ondiiik/meteoink/graphics/bitmap/png/gs/greetings.png

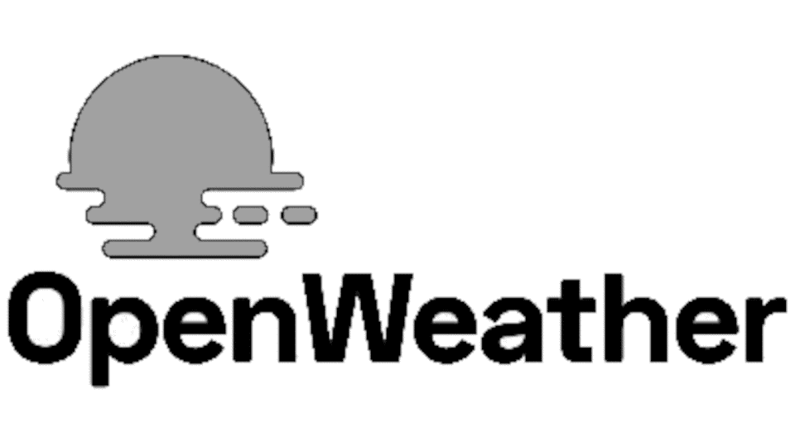
graphics/bitmap/png/gs/greetings.png
