ondiiik/meteoink/graphics/bitmap/wind/acep/wa430.png

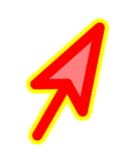
graphics/bitmap/wind/acep/wa430.png
