ondiiik/meteoink/graphics/bitmap/wind/acep/wa445.png

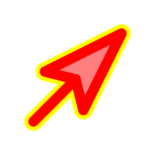
graphics/bitmap/wind/acep/wa445.png
