ondiiik/meteoink/graphics/bitmap/wind/acep/wa460.png

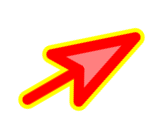
graphics/bitmap/wind/acep/wa460.png
