ondiiik/meteoink/graphics/bitmap/wind/acep/wa4120.png

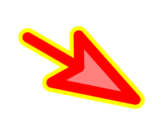
graphics/bitmap/wind/acep/wa4120.png
