ondiiik/meteoink/graphics/bitmap/wind/acep/wa4135.png

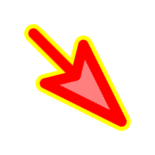
graphics/bitmap/wind/acep/wa4135.png
