ondiiik/meteoink/graphics/bitmap/wind/acep/wa4150.png

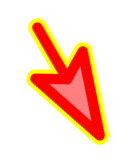
graphics/bitmap/wind/acep/wa4150.png
