ondiiik/meteoink/graphics/bitmap/wind/acep/wa4210.png

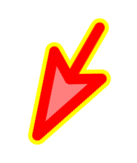
graphics/bitmap/wind/acep/wa4210.png
