ondiiik/meteoink/graphics/bitmap/wind/acep/wa4225.png

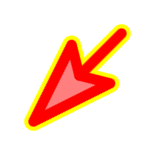
graphics/bitmap/wind/acep/wa4225.png
