ondiiik/meteoink/graphics/bitmap/wind/acep/wa4240.png

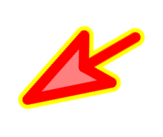
graphics/bitmap/wind/acep/wa4240.png
