ondiiik/meteoink/graphics/bitmap/wind/acep/wa4300.png

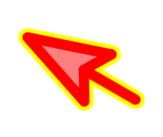
graphics/bitmap/wind/acep/wa4300.png
