ondiiik/meteoink/graphics/bitmap/wind/acep/wa4315.png

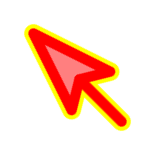
graphics/bitmap/wind/acep/wa4315.png
