ondiiik/meteoink/graphics/bitmap/wind/acep/wa4330.png

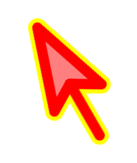
graphics/bitmap/wind/acep/wa4330.png
