ondiiik/meteoink/simulator/main.py

from os import stat

try:
    stat("bitmaps")

    from ulogging import getLogger, dump_exception

    logger = getLogger("main")

    try:
        logger.info("Starting the application ...")
        from app import run

        run()

    except KeyboardInterrupt as e:
        logger.info("Interrupted by keyboard ...")
    except BaseException as e:
        dump_exception("!!! APPLICATION ERROR - REBOOTING !!!", e)
        import machine

        machine.reset()
except OSError:
    print("##############################################")
    print("### Please upload bitmaps (folder bitmaps) ###")
    print("##############################################")
