ondiiik/meteoink/simulator/web/page/index.py

from ulogging import getLogger

logger = getLogger(__name__)

from config import beep, location, connection, spot, temp, vbat, behavior, time, api
from battery import battery
from lang import trn
import web


def index(page):
    _pg_loc(page)
    _pg_wifi(page)
    _pg_set(page)

    page.heading(2, trn("Misc"))
    page.button(trn("Go to travel mode"), "zzz")
    page.button(trn("Go to normal mode"), "reset")


def _pg_loc(page):
    page.heading(2, trn("Locations setup"))

    with page.table(
        (trn("Location"), trn("Latitude"), trn("Longitude"), "", ""),
        'frame="hsides"',
        'style="text-align:left"',
    ) as table:
        for i in location["locations"]:
            idx = {"idx": location["locations"].index(i)}
            table.row(
                (
                    i["name"],
                    f"{i['lat']:.7f}N",
                    f"{i['lon']:.7f}E",
                    web.button(trn("Edit"), "locedt", idx),
                    web.button(trn("Delete"), "locdlt", idx),
                ),
                web.SPACES,
            )

    page.br()
    page.button(trn("Add new location"), "locnew")
    page.br()


def _pg_wifi(page):
    page.heading(2, trn("WiFi setup"))
    with page.table(
        ("SSID", "BSSID", trn("Location"), "", ""),
        'frame="hsides"',
        'style="text-align:left"',
    ) as table:
        for i in connection["connections"]:
            if i["bssid"] is None:
                bssid = ""
            else:
                bssid = i["bssid"]

            idx = {"idx": connection["connections"].index(i)}
            loc = int(i["location"])
            table.row(
                (
                    i["ssid"],
                    bssid,
                    (
                        location["locations"][loc]["name"]
                        if loc < len(location["locations"])
                        else "..."
                    ),
                    web.button(trn("Edit"), "wifiedt", idx),
                    web.button(trn("Delete"), "wifidlt", idx),
                ),
                web.SPACES,
            )

    page.br()
    page.button(trn("Add new WiFi"), "wifinew")
    page.br()


def _pg_set(page):
    page.heading(2, trn("Confort temperatures"))
    with page.table(None, 'frame="hsides"') as table:
        table.row(
            (trn("Indoor high"), "{:.1f} °C".format(temp["indoor_high"])), web.SPACES
        )
        table.row(
            (trn("Outdoor high"), "{:.1f} °C".format(temp["outdoor_high"])), web.SPACES
        )
        table.row(
            (trn("Outdoor low"), "{:.1f} °C".format(temp["outdoor_low"])), web.SPACES
        )
        table.row((web.button(trn("Edit temperatures"), "tempedt"), ""), web.SPACES)

    page.heading(2, trn("Alerts"))
    with page.table(None, 'frame="hsides"') as table:
        table.row(
            (
                trn("Outside temperature balanced"),
                web.button_enable(beep["temp_balanced"], "alerttemp"),
            ),
            web.SPACES,
        )
        table.row(
            (
                trn("Software bug detected"),
                web.button_enable(beep["error_beep"], "alertbug"),
            ),
            web.SPACES,
        )

    page.heading(2, trn("General setup"))
    with page.table(None, 'frame="hsides"') as table:
        table.row(
            (trn("Summer time"), "", web.button_enable(not time["winter"], "summert")),
            web.SPACES,
        )
        table.row(
            (
                trn("Refresh time"),
                trn("{} min (doubled from {}:00 to {}:00)").format(
                    behavior["refresh"], behavior["dbl"][0], behavior["dbl"][1]
                ),
                web.button(trn("Edit"), "refredt"),
            ),
            web.SPACES,
        )
        table.row(
            (trn("Language"), api["language"], web.button(trn("Edit"), "langedt")),
            web.SPACES,
        )
        table.row((trn("Units"), api["units"], ""), web.SPACES)
        table.row(
            (
                trn("Variant"),
                trn("Two days" if api["variant"] == 2 else "Four days"),
                web.button(trn("Edit"), "variantedt"),
            ),
            web.SPACES,
        )
        table.row(
            ("API key", api["apikey"], web.button(trn("Edit"), "apiedt")), web.SPACES
        )

    page.heading(2, trn("Hotspot setup"))
    with page.table(None, 'frame="hsides"') as table:
        table.row(
            ("SSID", spot["ssid"], web.button(trn("Edit"), "ssidedt")), web.SPACES
        )
        table.row(
            (trn("Password"), spot["passwd"], web.button(trn("Edit"), "passedt")),
            web.SPACES,
        )

    page.heading(2, trn("Battery setup"))
    with page.table(None, 'frame="hsides"') as table:
        table.row(
            (trn("Current voltage"), "{:.2f} V".format(battery.voltage), ""), web.SPACES
        )
        table.row(
            (
                trn("Critical voltage"),
                "{:.2f} V".format(vbat["low_voltage"]),
                web.button(trn("Edit"), "battedt"),
            ),
            web.SPACES,
        )


@web.webpage_handler(__name__, "GET")
def www(page, args):
    index(page)


@web.webpage_handler(__name__, "POST")
def www(page, args):
    logger.debug(f'args: {", ".join([k+"="+v for k, v in args.items()])}')

    action = args.get("action", None)

    if action:
        web.actions[action](page, args)
    else:
        index(page)
